NewieVentures/Rosella/src/lora_button/inc/config.h

#ifndef __CONFIG_H__
#define __CONFIG_H__

// the active channel plan is the one that will be compiled
// options are :
//      CP_US915
//      CP_AU915
//      CP_EU868
//      CP_KR920
//      CP_AS923
//      CP_AS923_JAPAN
//      CP_IN865
#if !defined(CHANNEL_PLAN)
#define CHANNEL_PLAN CP_AU915
#endif

#endif
