NewieVentures/Rosella/src/lora_button/src/RadioEvent.cpp

#include <cstddef>
#include "RadioEvent.h"

RadioEvent::RadioEvent() {
    mOnRx = NULL;
}

void RadioEvent::setReceiveHandler(void (*onRx)(uint8_t *RxBuffer, 
                                                uint8_t RxBufferSize)) {
    mOnRx = onRx;
}

void RadioEvent::PacketRx(uint8_t port, 
                          uint8_t *payload, 
                          uint16_t size, 
                          int16_t rssi, 
                          int8_t snr, 
                          lora::DownlinkControl ctrl, 
                          uint8_t slot, 
                          uint8_t retries, 
                          uint32_t address, 
                          bool dupRx) {
    mDotEvent::PacketRx(port, payload, size, rssi, snr, ctrl, slot, retries, address, dupRx);

    if(port == 200 || port == 201 || port == 202) {
        Fota::getInstance()->processCmd(payload, port, size);
    }
}

/*!
 * MAC layer event callback prototype.
 *
 * \param [IN] flags Bit field indicating the MAC events occurred
 * \param [IN] info  Details about MAC events occurred
 */
void RadioEvent::MacEvent(LoRaMacEventFlags* flags, LoRaMacEventInfo* info) {
    if (mts::MTSLog::getLogLevel() == mts::MTSLog::TRACE_LEVEL) {
        std::string msg = "OK";
        switch (info->Status) {
            case LORAMAC_EVENT_INFO_STATUS_ERROR:
                msg = "ERROR";
                break;
            case LORAMAC_EVENT_INFO_STATUS_TX_TIMEOUT:
                msg = "TX_TIMEOUT";
                break;
            case LORAMAC_EVENT_INFO_STATUS_RX_TIMEOUT:
                msg = "RX_TIMEOUT";
                break;
            case LORAMAC_EVENT_INFO_STATUS_RX_ERROR:
                msg = "RX_ERROR";
                break;
            case LORAMAC_EVENT_INFO_STATUS_JOIN_FAIL:
                msg = "JOIN_FAIL";
                break;
            case LORAMAC_EVENT_INFO_STATUS_DOWNLINK_FAIL:
                msg = "DOWNLINK_FAIL";
                break;
            case LORAMAC_EVENT_INFO_STATUS_ADDRESS_FAIL:
                msg = "ADDRESS_FAIL";
                break;
            case LORAMAC_EVENT_INFO_STATUS_MIC_FAIL:
                msg = "MIC_FAIL";
                break;
            default:
                break;
        }
        logTrace("Event: %s", msg.c_str());

        logTrace("Flags Tx: %d Rx: %d RxData: %d RxSlot: %d LinkCheck: %d JoinAccept: %d",
                 flags->Bits.Tx, flags->Bits.Rx, flags->Bits.RxData, flags->Bits.RxSlot, flags->Bits.LinkCheck, flags->Bits.JoinAccept);
        logTrace("Info: Status: %d ACK: %d Retries: %d TxDR: %d RxPort: %d RxSize: %d RSSI: %d SNR: %d Energy: %d Margin: %d Gateways: %d",
                 info->Status, info->TxAckReceived, info->TxNbRetries, info->TxDatarate, info->RxPort, info->RxBufferSize,
                 info->RxRssi, info->RxSnr, info->Energy, info->DemodMargin, info->NbGateways);
    }

    if (flags->Bits.Rx) {
        logDebug("Rx %d bytes", info->RxBufferSize);
        if (info->RxBufferSize > 0 && mOnRx != NULL) {
            mOnRx(info->RxBuffer, info->RxBufferSize);
        }
    }
}
